OzSecICT/badge-adventure/include/config.hpp

#ifndef Config_hpp
#define Config_hpp

// Current firmware version
// This is compared to what is available online to determine if an update is needed
#define VERSION 2

// WiFi defaults
#define WIFI_SSID "OzSec 2024"
#define WIFI_PASSWORD "OzSec2024!"

#endif
